wpirri/DomPiWeb/Documentos/Esquema del proyecto/Esquema-General.png

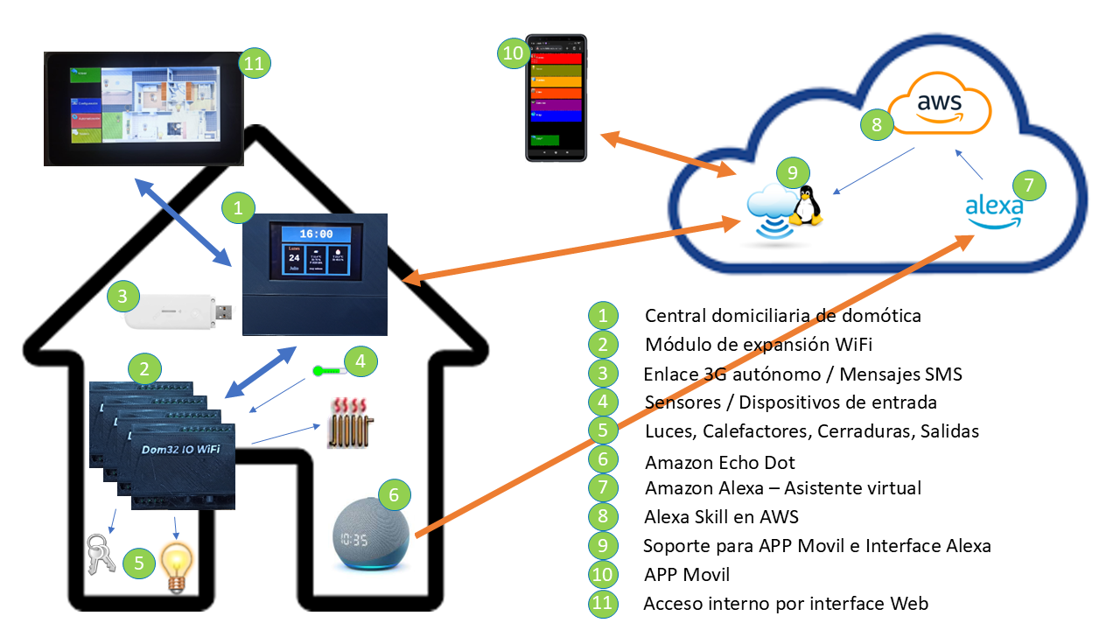
Documentos/Esquema del proyecto/Esquema-General.png
