wpirri/DomPiWeb/Documentos/20241027_184519.jpg

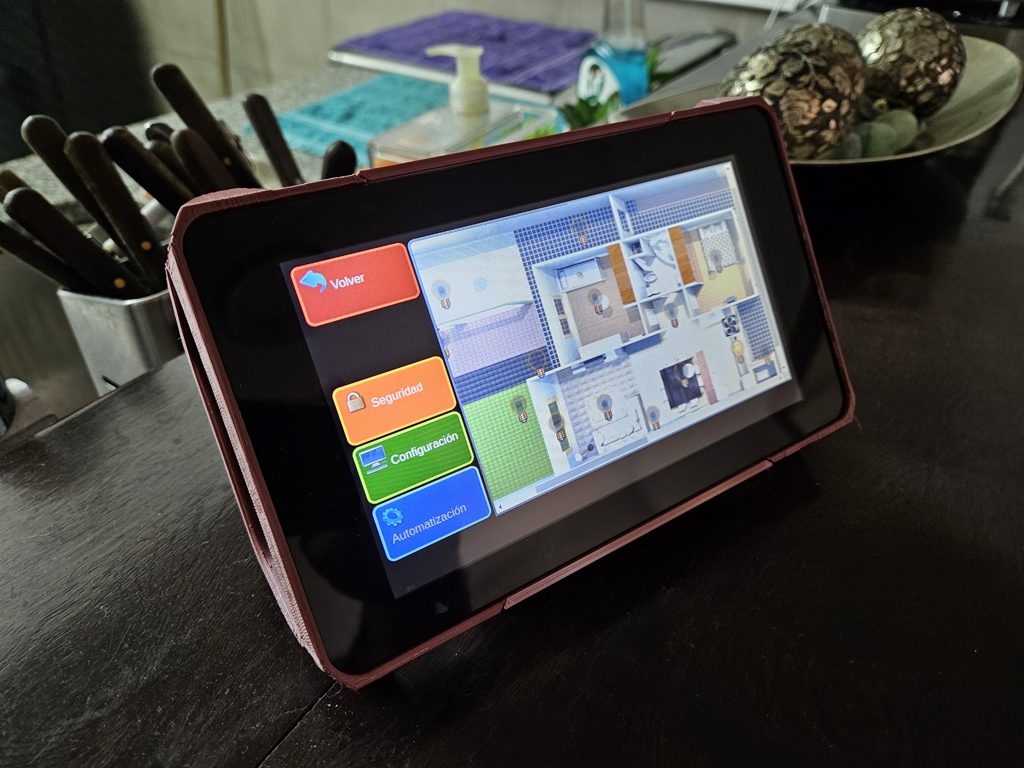
Documentos/20241027_184519.jpg
