wpirri/DomPiWeb/Circuito-IO/DomPiWeb.png

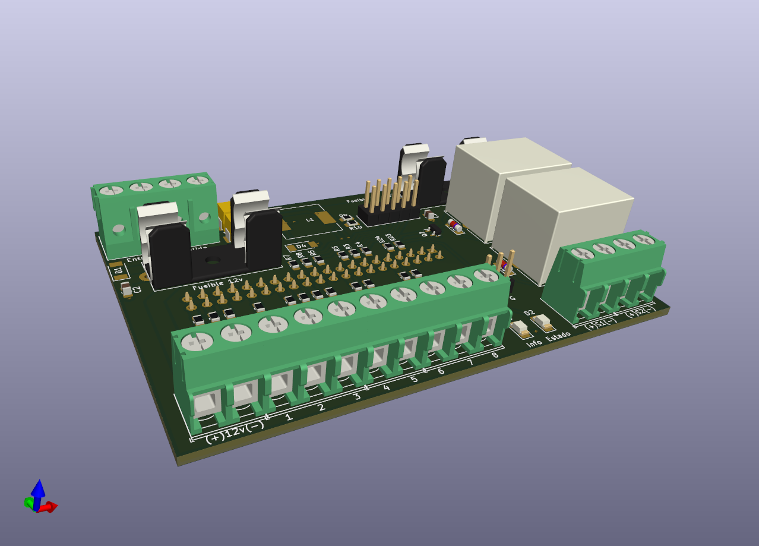
Circuito-IO/DomPiWeb.png
