wpirri/DomPiWeb/Documentos/2-focos-calefactor-extractor.png

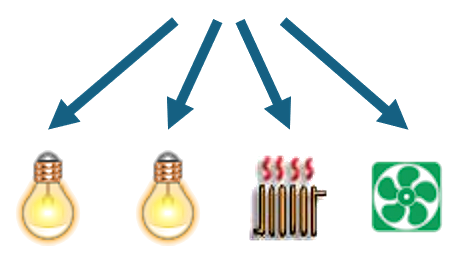
Documentos/2-focos-calefactor-extractor.png
