wpirri/DomPiWeb/Documentos/4-focos.png

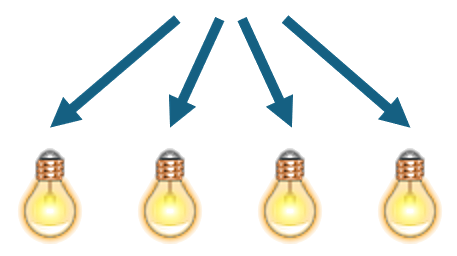
Documentos/4-focos.png
