wpirri/DomPiWeb/Documentos/4-riego.png

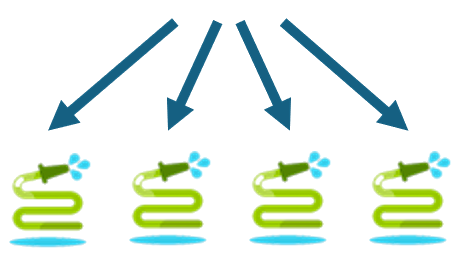
Documentos/4-riego.png
