wpirri/DomPiWeb/Documentos/4-switch-2-temp.png

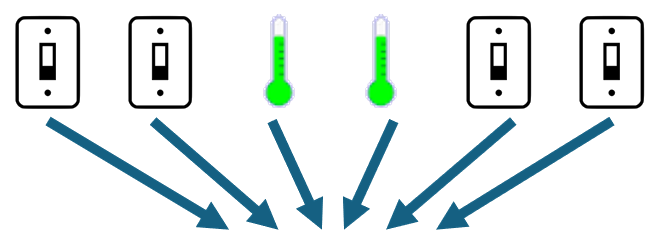
Documentos/4-switch-2-temp.png
