wpirri/DomPiWeb/Documentos/4-switch-temp-luz.png

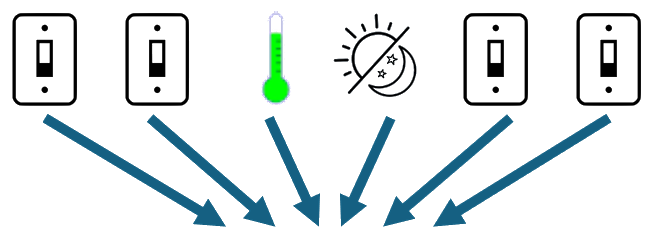
Documentos/4-switch-temp-luz.png
