wpirri/DomPiWeb/Documentos/6-switch.png

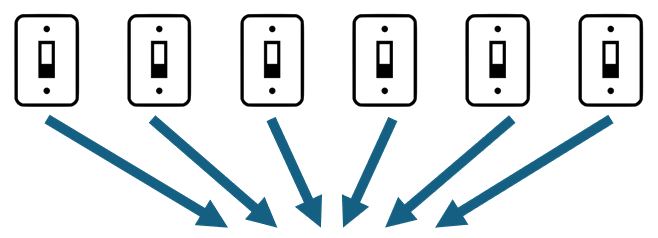
Documentos/6-switch.png
