wpirri/DomPiWeb/Documentos/central.png

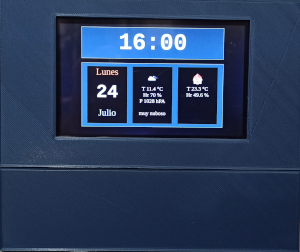
Documentos/central.png
