wpirri/DomPiWeb/Documentos/cloud.png

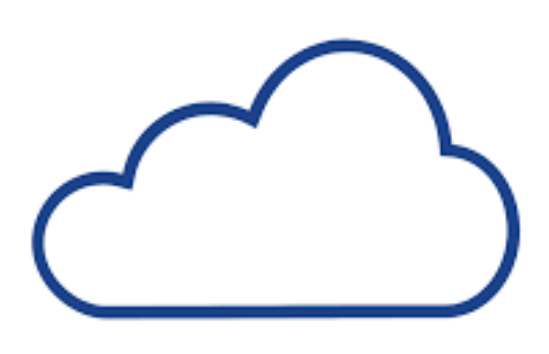
Documentos/cloud.png
