wpirri/DomPiWeb/Documentos/dom32-io-wifi.png

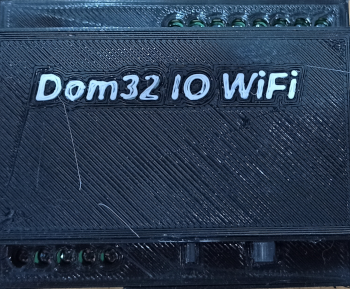
Documentos/dom32-io-wifi.png
