wpirri/DomPiWeb/Documentos/echo-dot.jpg

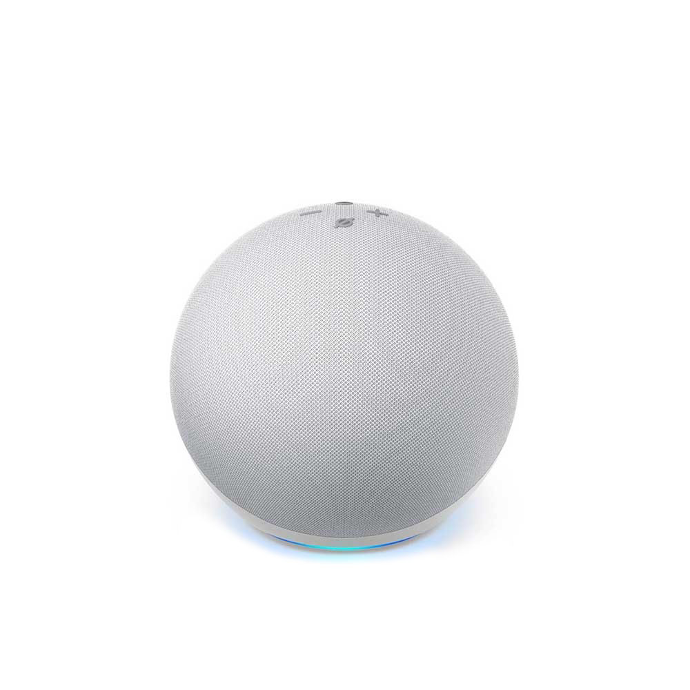
Documentos/echo-dot.jpg
