wpirri/DomPiWeb/Documentos/Esquema del proyecto/Imagenes/2023-07-24 16.00.49.jpg

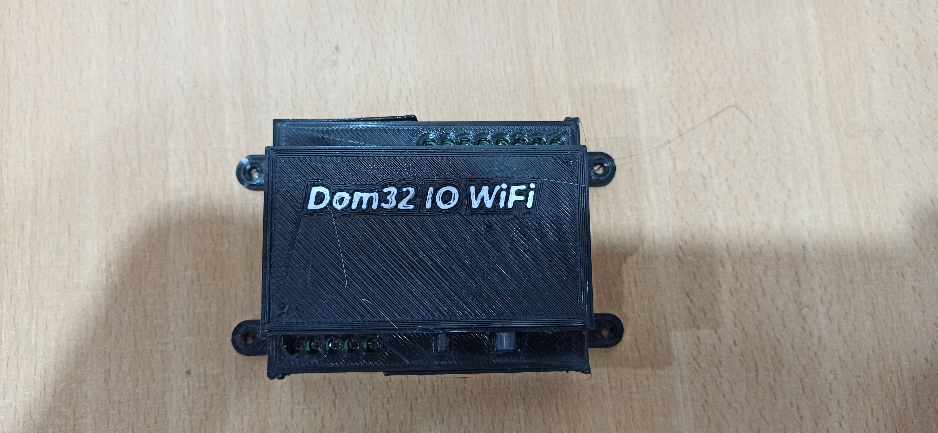
Documentos/Esquema del proyecto/Imagenes/2023-07-24 16.00.49.jpg
