wpirri/DomPiWeb/Documentos/Esquema del proyecto/Imagenes/linux-cloud.jpg

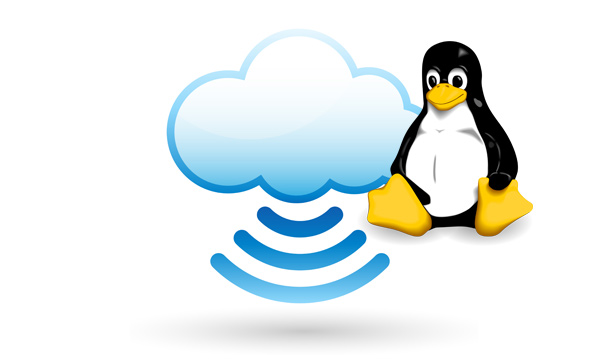
Documentos/Esquema del proyecto/Imagenes/linux-cloud.jpg
