wpirri/DomPiWeb/Documentos/Esquema del proyecto/Imagenes/modem-3g.png

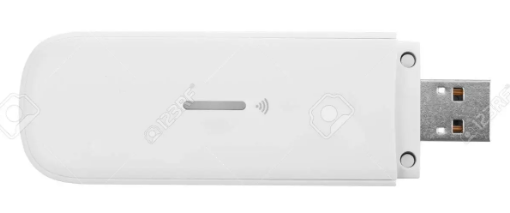
Documentos/Esquema del proyecto/Imagenes/modem-3g.png
