wpirri/DomPiWeb/Documentos/Esquema del proyecto/wifi-coretimer.png

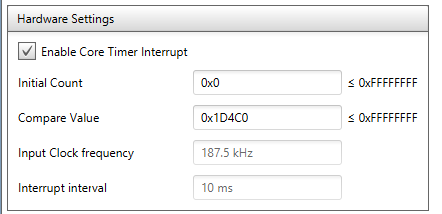
Documentos/Esquema del proyecto/wifi-coretimer.png
