wpirri/DomPiWeb/Documentos/Esquema del proyecto/wifi-int.png

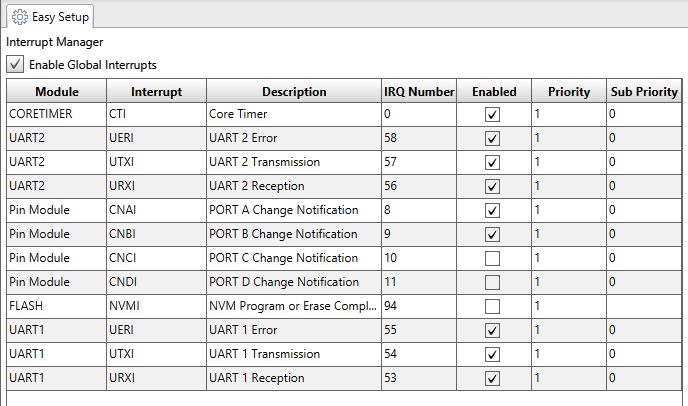
Documentos/Esquema del proyecto/wifi-int.png
