wpirri/DomPiWeb/Documentos/Esquema del proyecto/wifi-resources.png

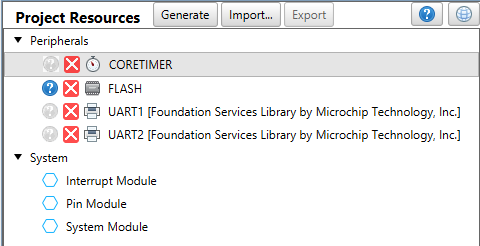
Documentos/Esquema del proyecto/wifi-resources.png
