wpirri/DomPiWeb/Documentos/Esquema del proyecto/wifi-system.png

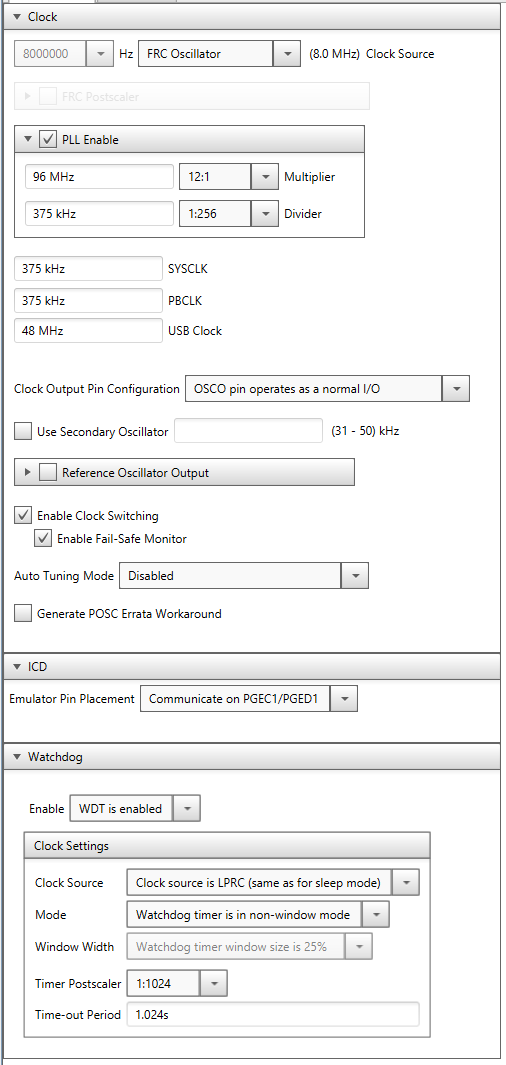
Documentos/Esquema del proyecto/wifi-system.png
