wpirri/DomPiWeb/Documentos/Esquema del proyecto/wifi-uart1.png

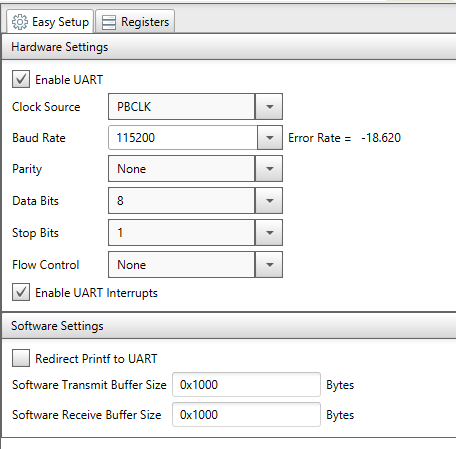
Documentos/Esquema del proyecto/wifi-uart1.png
