wpirri/DomPiWeb/Documentos/Esquema del proyecto/wifi-uart2.png

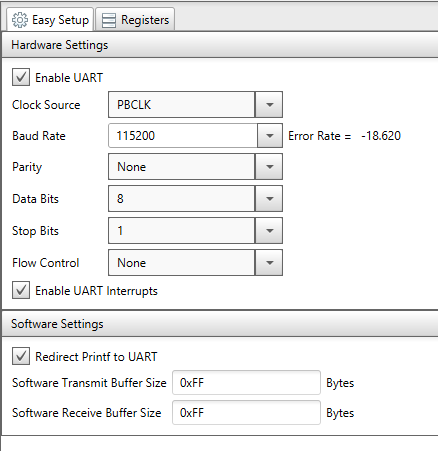
Documentos/Esquema del proyecto/wifi-uart2.png
