wpirri/DomPiWeb/Documentos/home2.jpg

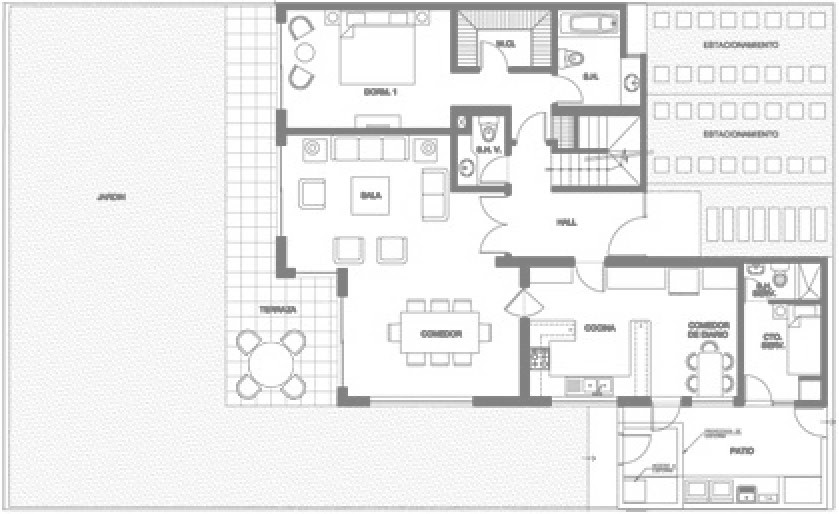
Documentos/home2.jpg
