wpirri/DomPiWeb/Documentos/home-term.png

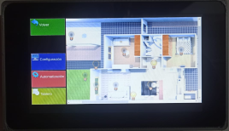
Documentos/home-term.png
