wpirri/DomPiWeb/Documentos/RaspBerryPi/Display/Adafruit-2260_Digikey-1528-1210-ND.png

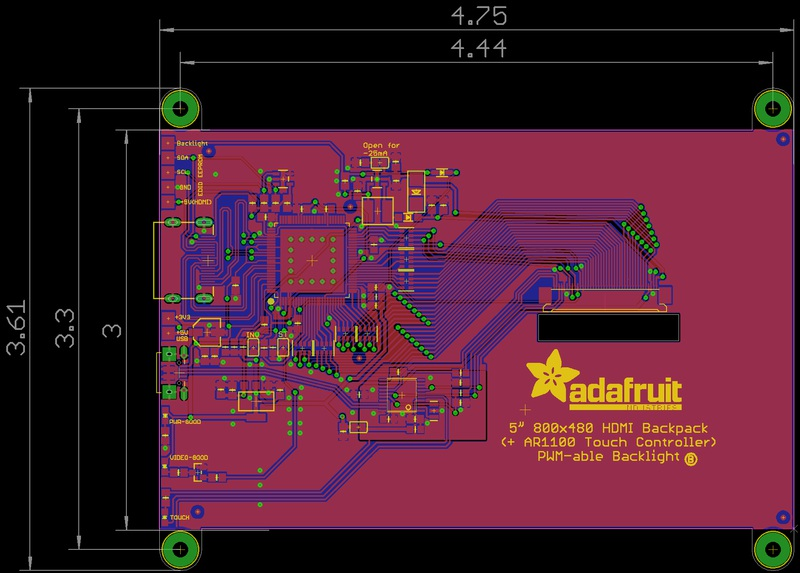
Documentos/RaspBerryPi/Display/Adafruit-2260_Digikey-1528-1210-ND.png
