wpirri/DomPiWeb/Documentos/RaspBerryPi/RBPi-USB-Ports.png

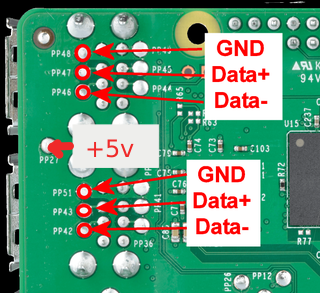
Documentos/RaspBerryPi/RBPi-USB-Ports.png
