wpirri/DomPiWeb/Documentos/Esquema del proyecto/Imagenes/DompiWeb32 - Montaje expandido.png

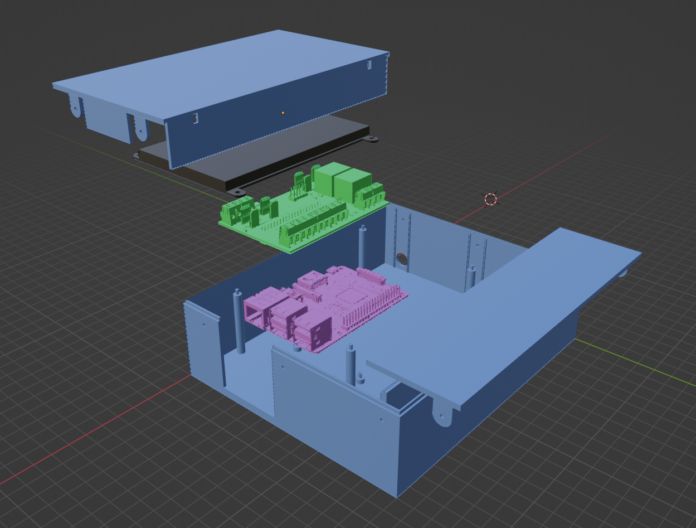
Documentos/Esquema del proyecto/Imagenes/DompiWeb32 - Montaje expandido.png
