wpirri/DomPiWeb/Documentos/Montaje-DomPiWeb.png

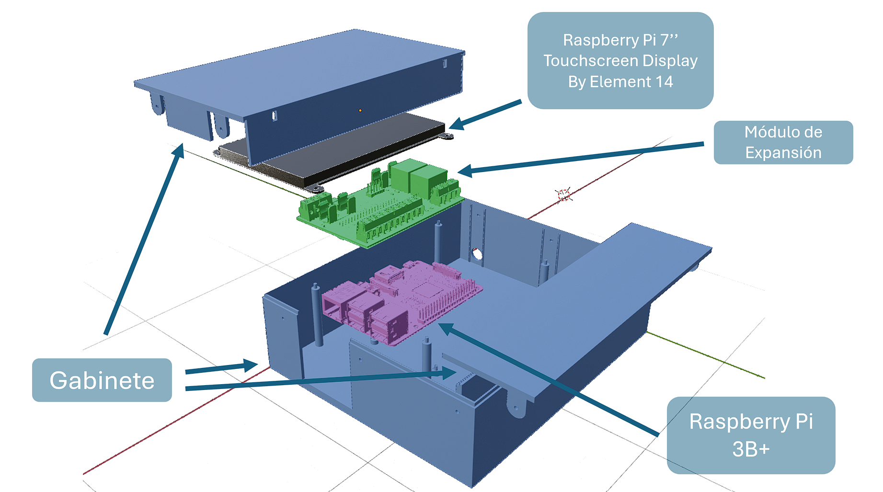
Documentos/Montaje-DomPiWeb.png
