wpirri/DomPiWeb/Gabinete/OpenSCAD/MontajeExpandido.png

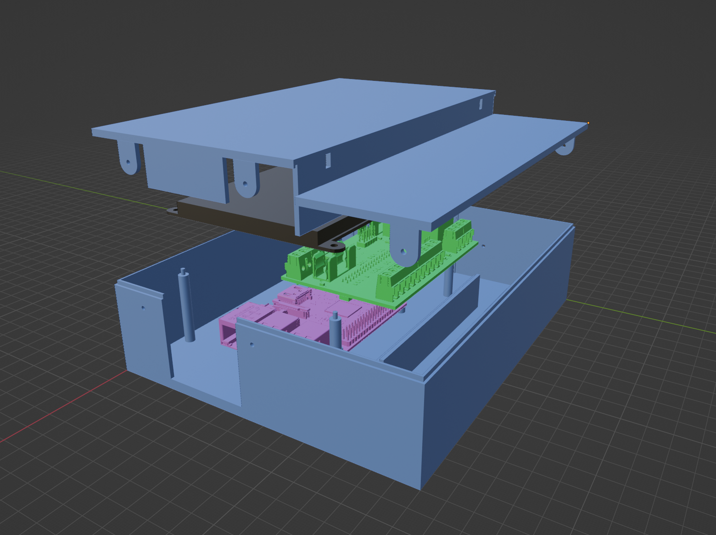
Gabinete/OpenSCAD/MontajeExpandido.png
