wpirri/DomPiWeb/Programas/Common/dom32iopi.h

/***************************************************************************
  Copyright (C) 2020   Walter Pirri
  This library is free software; you can redistribute it and/or
  modify it under the terms of the GNU Lesser General Public
  License as published by the Free Software Foundation; either
  version 2.1 of the License, or (at your option) any later version.
  This library is distributed in the hope that it will be useful,
  but WITHOUT ANY WARRANTY; without even the implied warranty of
  MERCHANTABILITY or FITNESS FOR A PARTICULAR PURPOSE.  See the GNU
  Lesser General Public License for more details.
  You should have received a copy of the GNU Lesser General Public
  License along with this library; if not, write to the Free Software
  Foundation, Inc., 59 Temple Place, Suite 330, Boston, MA  02111-1307  USA
 ***************************************************************************/
#ifndef _DOM32IOPI_H_
#define _DOM32IOPI_H_

#include <cstdio>

#define IO_ARRAY_LEN 24
#define IO_FILTER_STEPS 10

class Dom32IoPi
{
public:
    typedef struct _pi_data
    {
        struct
        {
            struct
            {
                char ap1[33];
                char ap1_pass[33];
                char ap2[33];
                char ap2_pass[33];
                char host1[33];
                char host2[33];
                unsigned int host1_port;
                unsigned int host2_port;
                char host1_protocol[9];
                char host2_protocol[9];
                char rqst_path[33];
                char hw_mac[13];
            } comm;
            struct 
            {
                unsigned char config;    /* 0=output 1=input 2=analog */
                unsigned char map;       /* Mapeo a pin de RaspBerry Pi */
            } port[IO_ARRAY_LEN];
            int default_config;
        } config;
        struct
        {
            struct
            {
                unsigned char ap1;
                unsigned char ap2;
                unsigned char lan1;
                unsigned char gsm1;
                unsigned char host1;
                unsigned char host2;
            } comm;
            struct 
            {
                unsigned char filter;
                unsigned char status;    /* 0/1 o analog */
                unsigned char change;    /* 0=sin cambio 1=cambio */
            } port[IO_ARRAY_LEN];
        } status;
    } pi_data;

	Dom32IoPi();
	Dom32IoPi(const char* filename);
	virtual ~Dom32IoPi();

    void LoadConfig( const char* filename = nullptr );

    int GetIOStatus();
    void SetIOStatus();
    int SetIO(const char* io, const char* sval);

    int GetConfig(int port, int *ioconfig);
    int ConfigIO(const char* io, const char* mode);

    void SetStatusLed(int st);
    void SetModeLed(int st);

    int HttpRespCode(const char* http);
    int HttpData(const char* http, char* data);


    pi_data m_pi_data;

protected:
    void SetDefaultConfig( void );
    void SetConfig( void );
    void SaveConfig( void );

    int m_sfd; 
    char m_config_file_name[FILENAME_MAX+1];

};

#endif /* _DOM32IOPI_H_ */
