wpirri/DomPiWeb/Programas/Common/queue.c

/***************************************************************************
    Copyright (C) 2013   Walter Pirri

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
    You should have received a copy of the GNU Lesser General Public
    License along with this library; if not, write to the Free Software
    Foundation, Inc., 59 Temple Place, Suite 330, Boston, MA  02111-1307  USA
 ***************************************************************************/
#include <stdio.h>
#include <stdlib.h>
#include <limits.h>
#include <string.h>

#include "queue.h"

typedef struct _QUEUE_ELEMENT
{
    unsigned char first;
    unsigned char last;
    unsigned char count;
    unsigned char elements;
    unsigned int len;
    void *buffer;
} QUEUE_ELEMENT;

QUEUE_ELEMENT g_queue_list_buffer[MAX_QUEUE_COUNT];

void QueueNextItem(unsigned char id, unsigned char *idx);

void QueueInit( void )
{
    unsigned char i;
    
    for(i = 0;i < MAX_QUEUE_COUNT; i++)
    {
        g_queue_list_buffer[i].buffer = NULL;
    }
}

unsigned char QueueOpen(unsigned char elements, unsigned int len, void* buffer)
{
    unsigned char i;
    
    for(i = 0;i < MAX_QUEUE_COUNT; i++)
    {
        if(g_queue_list_buffer[i].buffer == NULL) break;
    }
    if(i < MAX_QUEUE_COUNT)
    {
        g_queue_list_buffer[i].buffer = buffer;
        g_queue_list_buffer[i].elements = elements;
        g_queue_list_buffer[i].len = len;
        g_queue_list_buffer[i].first = 0;
        g_queue_list_buffer[i].last = 0;
        g_queue_list_buffer[i].count = 0;
        return i;
    }
    return (INVALID_QUEUE);
}

void QueueClose(unsigned char id)
{
    if(id < MAX_QUEUE_COUNT)
    {
        g_queue_list_buffer[id].buffer = NULL;
    }    
}

bool QueueAdd(unsigned char id, void* data)
{
    if(id < MAX_QUEUE_COUNT)
    {
        if(g_queue_list_buffer[id].count < g_queue_list_buffer[id].elements)
        {
            memcpy((g_queue_list_buffer[id].buffer + (g_queue_list_buffer[id].last * g_queue_list_buffer[id].len)),
                    data,
                    g_queue_list_buffer[id].len);
            QueueNextItem(id, &g_queue_list_buffer[id].last);
            g_queue_list_buffer[id].count++;
            return true;
        }
    }    
    return false;
}

bool QueueView(unsigned char id, void** data)
{
    if(id < MAX_QUEUE_COUNT)
    {
        if(g_queue_list_buffer[id].count)
        {
            *data =  (g_queue_list_buffer[id].buffer + (g_queue_list_buffer[id].first * g_queue_list_buffer[id].len));
            return true;
        }
    }    
    return false;
}

bool QueueGet(unsigned char id, void* data)
{
    if(id < MAX_QUEUE_COUNT)
    {
        if(g_queue_list_buffer[id].count)
        {
            memcpy( data,
                    (g_queue_list_buffer[id].buffer + (g_queue_list_buffer[id].first * g_queue_list_buffer[id].len)),
                    g_queue_list_buffer[id].len);
            QueueNextItem(id, &g_queue_list_buffer[id].first);
            g_queue_list_buffer[id].count--;
            return true;
        }
    }    
    return false;
}

bool QueueDel(unsigned char id)
{
    if(id < MAX_QUEUE_COUNT)
    {
        if(g_queue_list_buffer[id].count)
        {
            QueueNextItem(id, &g_queue_list_buffer[id].first);
            g_queue_list_buffer[id].count--;
            return true;
        }
    }    
    return false;
}

unsigned char QueueCount(unsigned char id)
{
    return g_queue_list_buffer[id].count;
}

void QueueNextItem(unsigned char id, unsigned char *idx)
{
    (*idx)++;
    if((*idx) >= g_queue_list_buffer[id].elements) (*idx) = 0;
}
