wpirri/DomPiWeb/Programas/Common/defines.h

#ifndef _DEFINES_H_
#define _DEFINES_H_

#define TIPO_HW_NINGUNO 0
#define TIPO_HW_WIFI    1
#define TIPO_HW_RBPI    2
#define TIPO_HW_DSC     3
#define TIPO_HW_GARNET  4
#define TIPO_HW_TOUCH   5



#endif /* _DEFINES_H_ */
